SurvivalHacking/Meteovision/3d/Meteovision NEW ICON 5.8/SOLE/Sole_Cover_Bianco.3mf

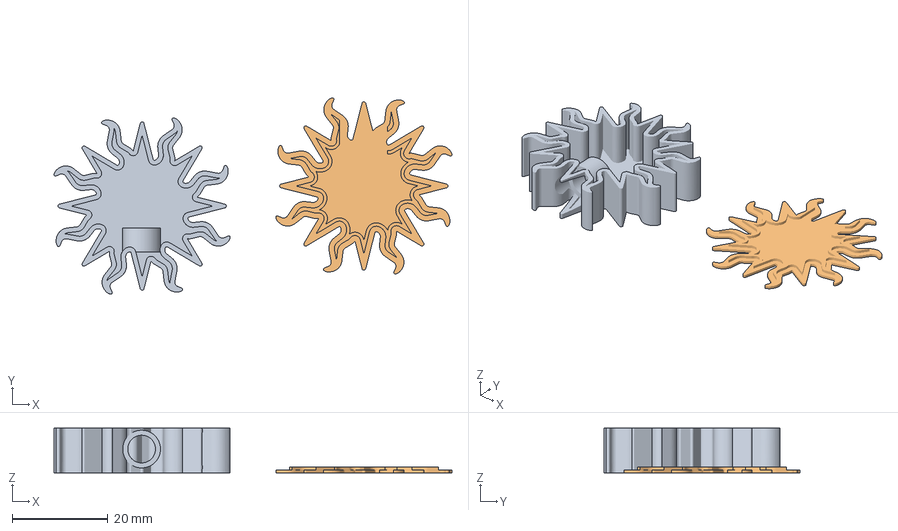
[picture p16: CAD file, 2025-12-09]
3d/Meteovision NEW ICON 5.8/SOLE/Sole_Cover_Bianco.3mf
83.3 x 41.1 x 9.40 mm
Sole_Base_Bianco.stl
Sole_Cover_Bianco.stl
