SurvivalHacking/Meteovision/3d/Elementi (BIANCHI).stl

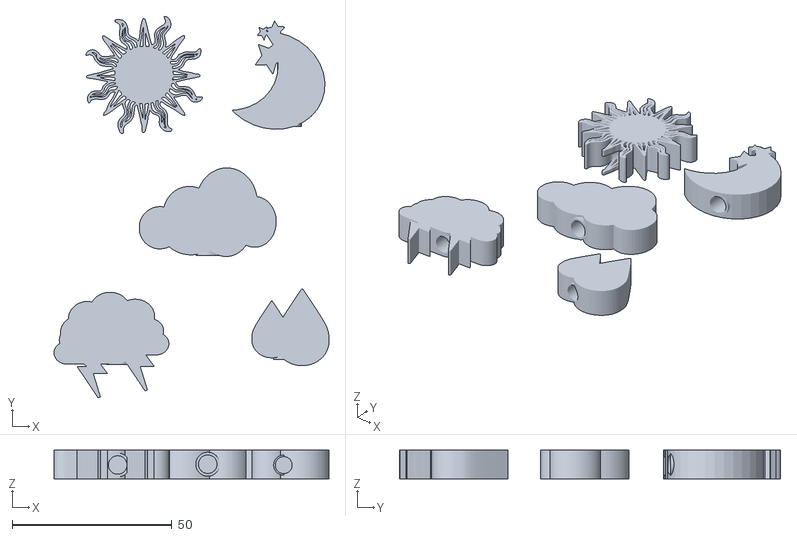
[picture p17: CAD file, 2025-09-04]
3d/Elementi (BIANCHI).stl
86.1 x 119.5 x 9.00
