SurvivalHacking/Meteovision/3d/Meteovision NEW ICON 5.8/NUVOLA/Nuvola2_Base_Azzurro.stl

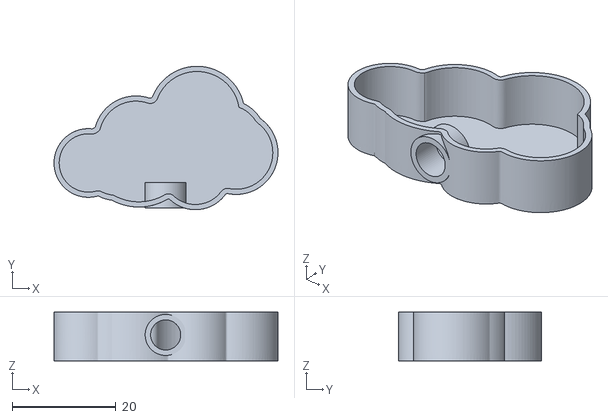
[picture p18: CAD file, 2025-12-09]
3d/Meteovision NEW ICON 5.8/NUVOLA/Nuvola2_Base_Azzurro.stl
43.1 x 27.6 x 9.40
