SurvivalHacking/Meteovision/3d/Meteovision NEW ICON 5.8/PIOGGIA/Gocce_Base_Bianco.stl

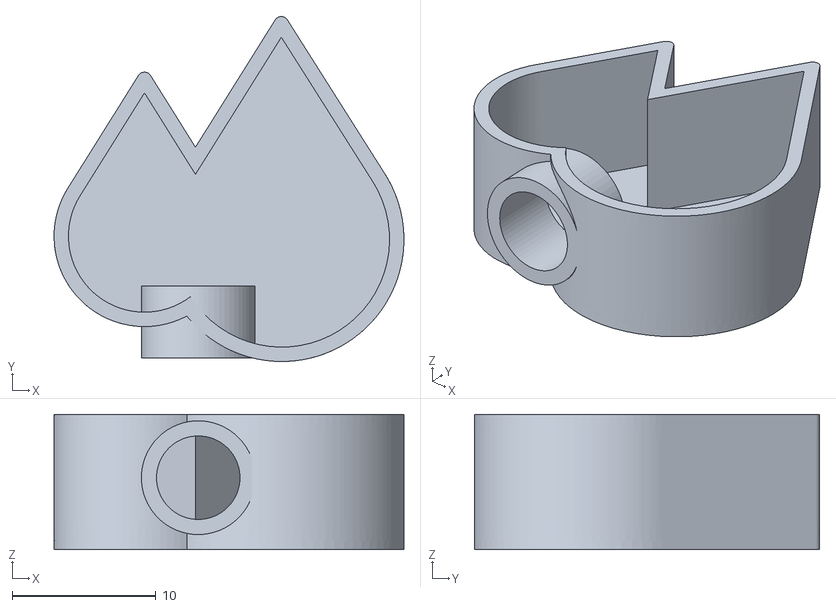
[picture p19: CAD file, 2025-12-09]
3d/Meteovision NEW ICON 5.8/PIOGGIA/Gocce_Base_Bianco.stl
24.3 x 24.0 x 9.40
