SurvivalHacking/Meteovision/3d/Anello (Traparente).stl

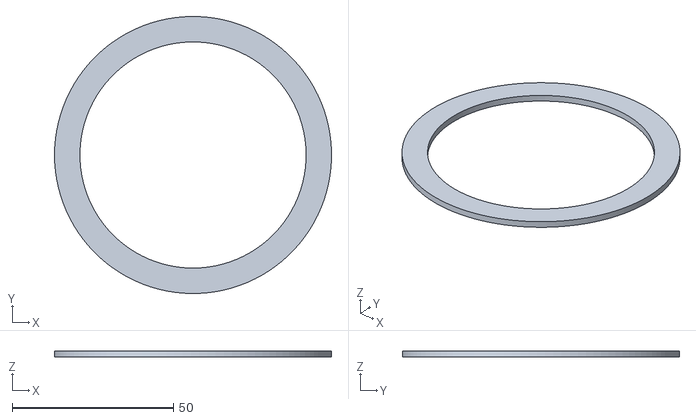
[picture p20: CAD file, 2025-09-04]
3d/Anello (Traparente).stl
86.0 x 86.0 x 2.00
