SurvivalHacking/Meteovision/3d/Elementi COLOR/BAMBU/Gocce (BLU-BIANCO) Bambu.3mf

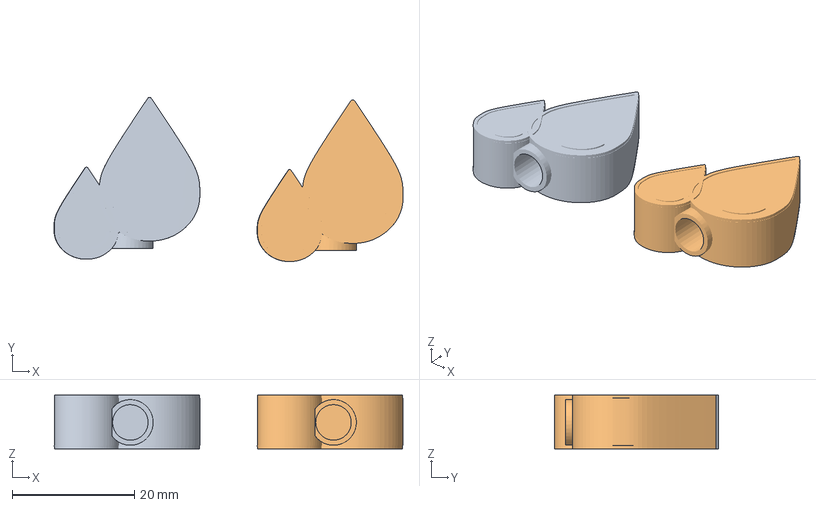
[picture p21: CAD file, 2025-09-04]
3d/Elementi COLOR/BAMBU/Gocce (BLU-BIANCO) Bambu.3mf
57.0 x 26.8 x 8.80 mm
Goccia Color x 2
